brianamos1/DuotrigesimalWS2811/images/Controller_T41_rev0.2a.png

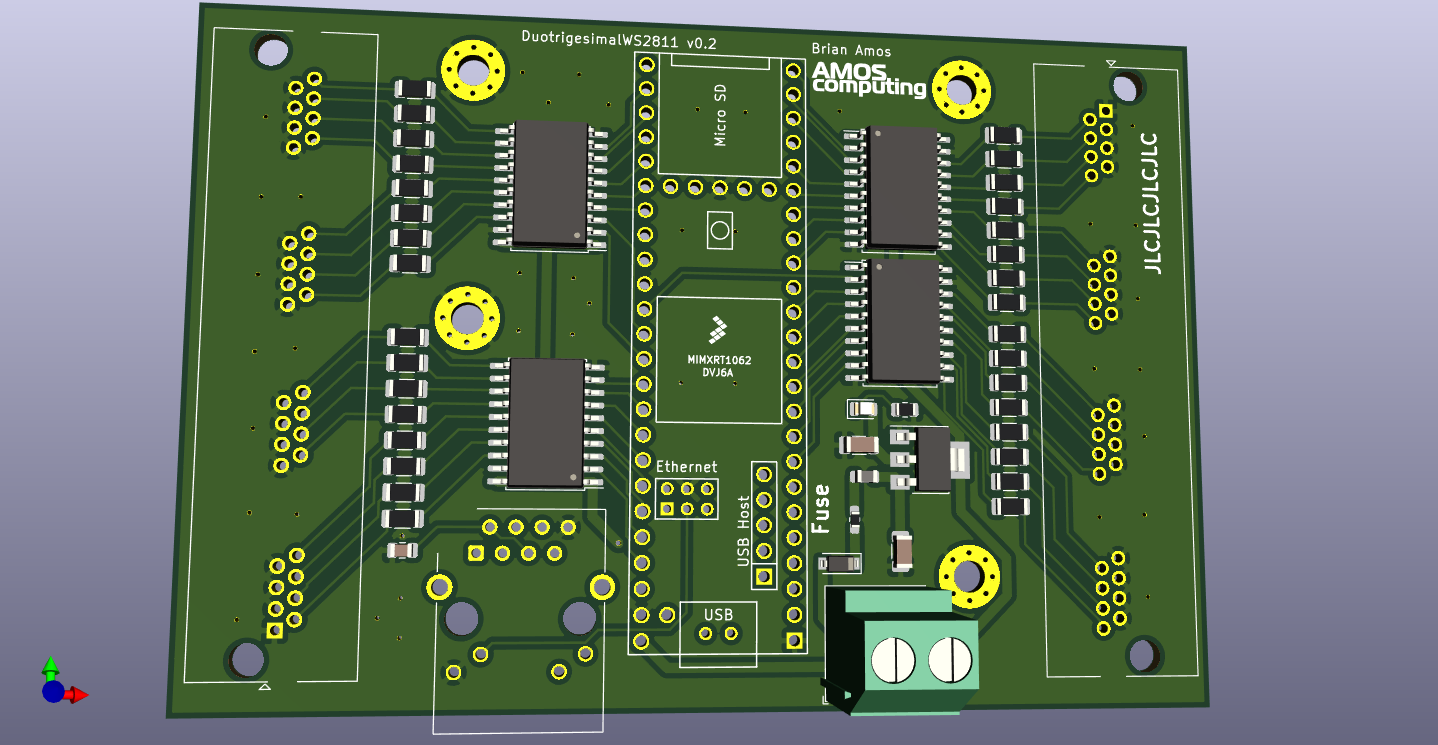
images/Controller_T41_rev0.2a.png
