brianamos1/DuotrigesimalWS2811/Splitter-0.3/images/splitter0.2-bare-back.png

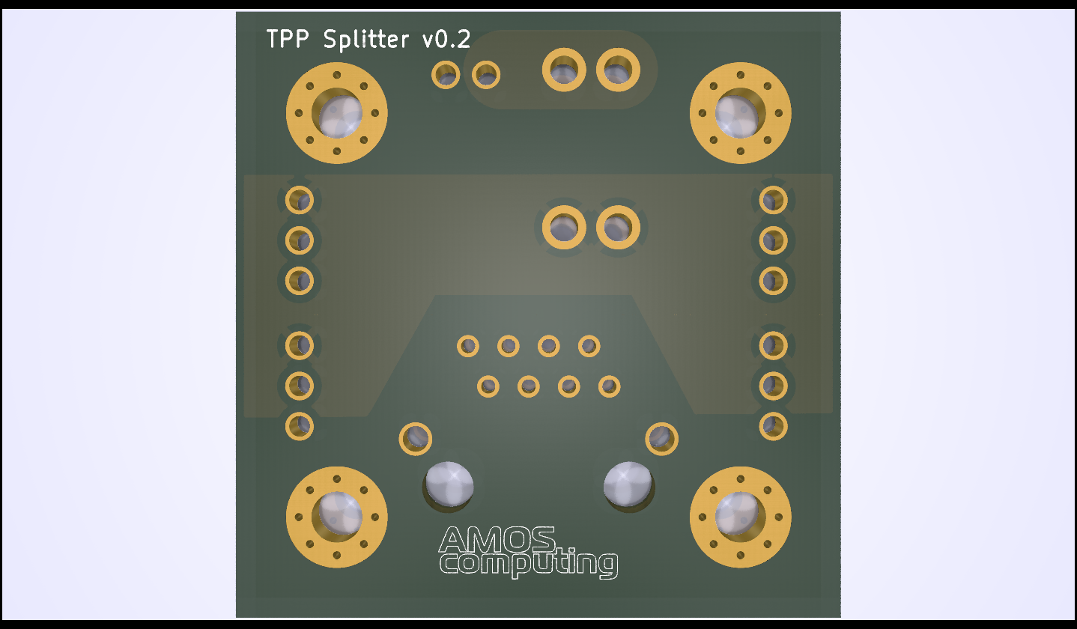
Splitter-0.3/images/splitter0.2-bare-back.png
