brianamos1/DuotrigesimalWS2811/Splitter-0.3/images/splitter0.3-bare-front.png

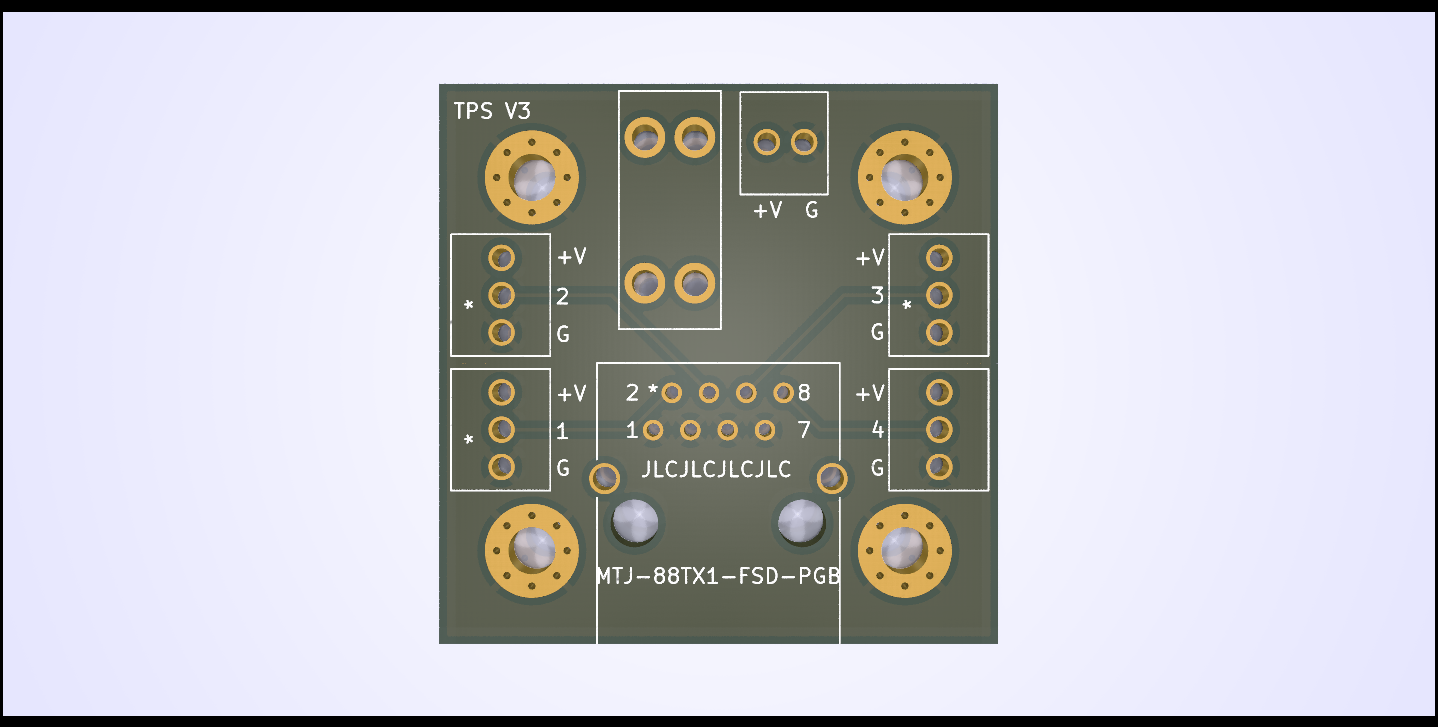
Splitter-0.3/images/splitter0.3-bare-front.png
